Willeye-uk/RetroLogic/png/Mainboard.png

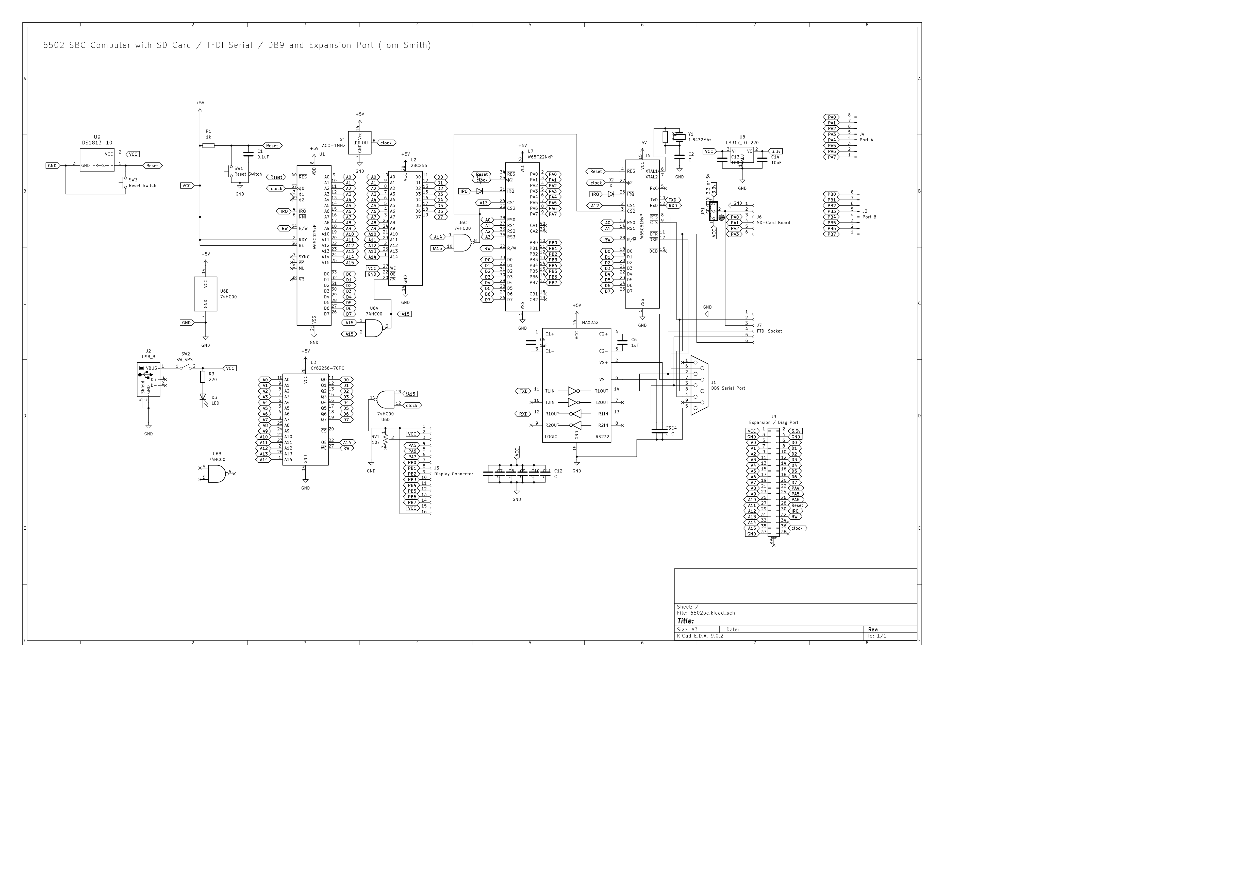
png/Mainboard.png
